pgreendale/MIDIFootPedal/Schematic/FootOrgan_Circuits.kicad_sch

## KiCad design Schematic/FootOrgan_Circuits.kicad_sch (2023-01-07)

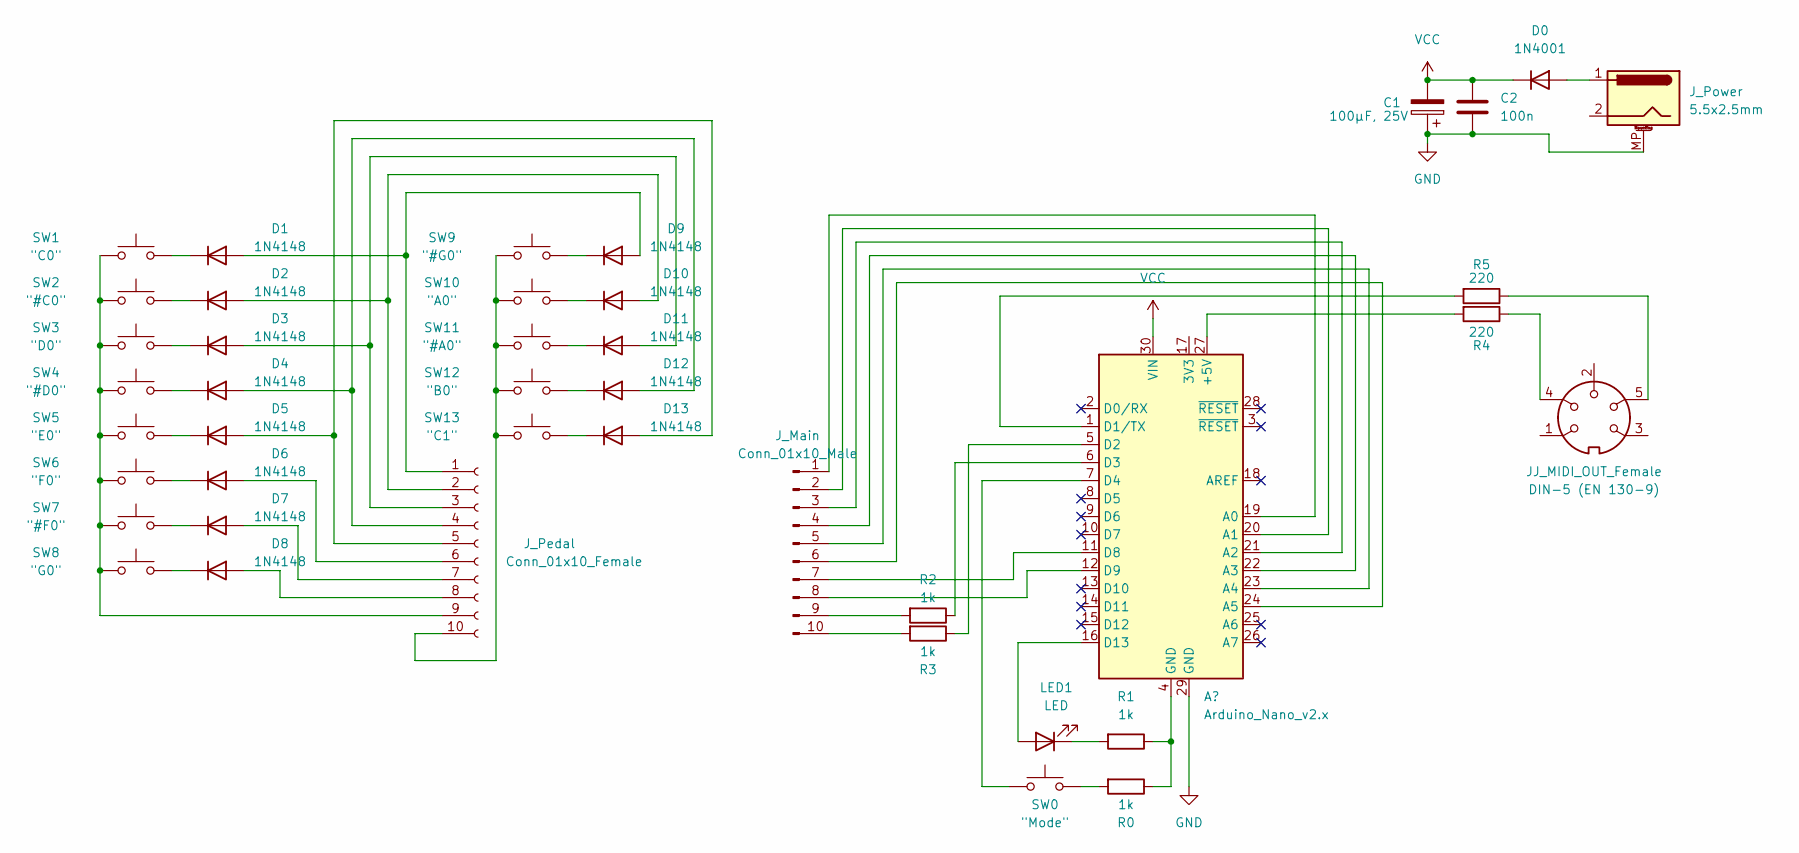
[picture p4: schematic FootOrgan_Circuits.kicad_sch]

Parts:
C1: 100µF, 25V
C2: 100n
D0: 1N4001; D_DO-41_SOD81_P10.16mm_Horizontal
D1, D2, D3, D4, D5, D6, D7, D8, D9, D10, D11, D12, D13: 1N4148; D_DO-35_SOD27_P7.62mm_Horizontal
JJ_MIDI_OUT_Female: DIN-5 (EN 130-9)
J_Main: Conn_01x10_Male
J_Pedal: Conn_01x10_Female
J_Power: 5.5x2.5mm
LED1: LED
R0, R1, R2, R3: 1k
R4, R5: 220
SW0: "Mode"
SW1: "C0"
SW2: "#C0"
SW3: "D0"
SW4: "#D0"
SW5: "E0"
SW6: "F0"
SW7: "#F0"
SW8: "G0"
SW9: "#G0"
SW10: "A0"
SW11: "#A0"
SW12: "B0"
SW13: "C1"

Connections:
unnamed: C1.1, C2.2, J_Power.MP (MountPin)
unnamed: C1.2, C2.1, D0.1 (K)
unnamed: D0.2 (A), J_Power.1
unnamed: D1.1 (K), SW1.2
unnamed: D1.2 (A), D9.2 (A), J_Pedal.1
unnamed: D2.1 (K), SW2.2
unnamed: D3.1 (K), SW3.2
unnamed: D4.1 (K), SW4.2
unnamed: D5.1 (K), SW5.2
unnamed: D6.1 (K), SW6.2
unnamed: D6.2 (A), J_Pedal.6
unnamed: D7.1 (K), SW7.2
unnamed: D7.2 (A), J_Pedal.7
unnamed: D8.1 (K), SW8.2
unnamed: D8.2 (A), J_Pedal.8
unnamed: D9.1 (K), SW9.2
unnamed: D10.1 (K), SW10.2
unnamed: D2.2 (A), D10.2 (A), J_Pedal.2
unnamed: D11.1 (K), SW11.2
unnamed: D3.2 (A), D11.2 (A), J_Pedal.3
unnamed: D12.1 (K), SW12.2
unnamed: D4.2 (A), D12.2 (A), J_Pedal.4
unnamed: D13.1 (K), SW13.2
unnamed: D5.2 (A), D13.2 (A), J_Pedal.5
unnamed: JJ_MIDI_OUT_Female.4, R4.1
unnamed: JJ_MIDI_OUT_Female.5, R5.1
unnamed: J_Main.9, R2.2
unnamed: J_Main.10, R3.2
unnamed: J_Pedal.9, SW1.1, SW2.1, SW3.1, SW4.1, SW5.1, SW6.1, SW7.1, SW8.1
unnamed: J_Pedal.10, SW9.1, SW10.1, SW11.1, SW12.1, SW13.1
unnamed: LED1.1 (K), R1.2
unnamed: R0.1, R1.1
unnamed: R0.2, SW0.2
